fishPointer/Joule-Thief/LTSpice/Joule Thief R4 V1.asc

C1: cap; 1µ
C2: cap; 10µ
C3: cap; 4.7µ
C4: cap; 10µ
C5: cap; 50m
C6: cap; 10n
D1: diode
D2: diode
D3: schottky; 1N5817
I1: current; {ISOURCE}
I2: current; {ISINK}
L1: ind; 20µ; Rser=1.87
M1: pmos; IRF9540N
R1: res; 900k
R2: res; 220k
R3: res; 47k
R4: res; 0.1
R5: res; 100k
R6: res; 0.1
R7: res; 4.7k
R8: res; 100k
R9: res; 75k
R10: res; 100
U1: LTC3105
U2: TL431
U3: lm393
V1: voltage; 1.2; Rser=0
V2: voltage; 0
Named nets: 0, IN, LDO, FB, OUT, vb
Joule Thief R4 V1 - MVP
.param ISINK=1m
.param ISOURCE=1
CURRENT LIMITED VOLTAGE SOURCE
.tran 1 startup
18650 Li-Ion Cell
AA 1.5V Alkaline Cell
4.3V Overcharge Protect
Dummy Load for testing
MPPC Resistor
AA ESR
Dummy Load for testing
