fishPointer/Joule-Thief/LTSpice/Accessory Circuits/Barebones BMS R0 - Comparators.asc

C1: cap; 10µ
LED1: diode; 1N914
LED: diode; 1N914
R1: res; 220
R2: res; 100
R3: res; 50k
R4: res; 220
R5: res; 500
R6: res; 50k
R7: res; 220
R8: res; 220
R9: res; 500
R10: res; 500
R11: res; 1k
R12: res; 220
R13: res; 1k
R14: res; 1k
R15: res; 1k
U1: TL431
U2: lm393
U3: 1N4728A
U4: lm393
U5: 1N4731A
U6: irf4905
U7: irfz44n
U8: LM358
U9: TL431
U10: lm393
V1: voltage; 4.2
V2: voltage; SINE(2.5 2.5 500)
V3: voltage; SINE(3 3 500)
V4: voltage; SINE(2.5 2.5 500)
Named nets: 0, VCC, VOUT, V431
.tran 20m
