fishPointer/Joule-Thief/LTSpice/Accessory Circuits/Charge and Discharge Protection R1V1.asc

C1: cap; 10n
C2: cap; 10n
M1: pmos; Si9433DY
M2: pmos; Si9433DY
M3: pmos; Si9433DY
M4: pmos; Si9433DY
R1: res; 10k
R2: res; 5k
R3: res; 1000
R4: res; 1400
R5: res; 100
R6: res; 220
R7: res; 50k
R8: res; 10
R9: res; 10
R10: res; 100
R11: res; 5k
R12: res; 10k
R13: res; 1000
R14: res; 1400
R15: res; 220
R16: res; 50k
U1: TL431
U2: lm393
U3: TL431
U4: lm393
V1: voltage; PULSE(0 5 0 20m 20m 20m 80m)
V2: voltage; 5
V3: voltage; 4.3
V4: voltage; PULSE(0 5 0 20m 20m 20m 80m)
V5: voltage; 5
V6: voltage; 4.3
Named nets: 0, VB, VA
.tran 80m startup
