fishPointer/Joule-Thief/LTSpice/Accessory Circuits/Charge and Discharge Protection R1V2.asc

C1: cap; 10n
M1: pmos; Si9433DY
M2: pmos; Si9433DY
R1: res; 10
R2: res; 100
R3: res; 5k
R4: res; 10k
R5: res; 1000
R6: res; 1400
R7: res; 220
R8: res; 50k
U1: TL431
U2: lm393
V1: voltage; PULSE(0 5 0 20m 20m 20m 80m)
V2: voltage; 5
V3: voltage; 4.3
Named nets: 0, VB, VA
.tran 100m
