fishPointer/Joule-Thief/LTSpice/Accessory Circuits/Current Limited Voltage Source.asc

C1: cap; 1µ
D1: diode
D2: diode
I1: current; {ISOURCE}
I2: current; {ISINK}
R1: res; 1k
V1: voltage; PULSE(0 10 0 1n 1n 1m 2m)
Named nets: 0
.param ISINK=1m
.param ISOURCE=1m
.tran 20m
CURRENT LIMITED VOLTAGE SOURCE
