fishPointer/Joule-Thief/LTSpice/Accessory Circuits/LM324 Output Impedance.asc

R1: res; 2k
R2: res; 2k
U1: LM324
U2: pot; T=0
U3: LM324
V2: voltage; 15
V3: voltage; 15
V_TEST1: voltage; SINE(); AC 1
V_TEST: voltage; SINE(); AC 1
Named nets: 15V, 0, -15V, V_OUT
.tran 0 20m 0 1m
.ac dec 100 0.1 100k
