fishPointer/Joule-Thief/LTSpice/Accessory Circuits/LM358 Schmitt Trigger V1.asc

M1: pmos
M2: nmos
R1: EuropeanResistor; 2k
R2: EuropeanResistor; 2k
R3: EuropeanResistor; 2k
R4: EuropeanResistor; 2k
R5: res; 1k
U1: LM358
V1: voltage; 5
V2: voltage; PULSE(0 5 0 50u 50u 10u 120u)
V3: voltage; 3.5
Named nets: 5V, 0, OUT, pulse
.tran 1m startup
