fishPointer/Joule-Thief/LTSpice/Accessory Circuits/LM386 Input Impedance.asc

C1: cap; 100µ
C2: cap; 100µ
C3: cap; 100n
C4: cap; 1000µ
R1: res; 8
U1: Lm386
U3: speaker
V1: voltage; 12
V2: voltage; SINE(0 1 1000); AC 1
Named nets: 0
LM386 AUDIO AMPLIFIER
.tran 0 10m 0 10u
.param T=0.5
.ac dec 100 1 100k
