fishPointer/Joule-Thief/LTSpice/Accessory Circuits/LM393 Schmitt Trigger V1.asc

C1: polcap; 1000µ; V=10 Irms=520m Rser=0.112 Lser=22.8n mfg="Würth Elektronik" pn="860020275015 WCAP-ATG5 10x12,5" type="Al electrolytic"
I1: current; 0.01
M2: pmos; AO6407
R1: res; 10k
R2: res; 30k
R4: res; 100
Rs: res; 5k
U1: lm393
U2: opamp
V2: voltage; 4.2
Named nets: 0, VCC
.tran 2 startup
.param Rp =(R1/R2)
.param R1=10k
.param R2=3.3k
BATTERY EXTRACTION MODULE
SAMPLING CAPACITOR VOLTAGE
FEEDING BACK INTO SCHMITT TRIGGER
SET SCHMITT TRIGGERS AT 1V, 4V
SCHMITT OUTPUT TOGGLES PMOS SWITCH
BMS HANDLES PULSE
