fishPointer/Joule-Thief/LTSpice/Accessory Circuits/NMOS Enable Switch Sketch.asc

M1: pmos; AO6407
R3: res; 10k
R_Load: res; 500
U1: 2N7000
V1: voltage; PULSE(0 5 0 1n 1n 10m 20m)
V2: voltage; 5
Named nets: 5V, 0, GPIO, out_n, out_p
.tran 100m
