fishPointer/Joule-Thief/LTSpice/Accessory Circuits/Rechargeable Battery V1.asc

B1: bi; I=I(V4)
BATT: bv; V=vbatt(V(vsoc))
CAP: cap; 100 IC=5; V=100
D1: diode
D2: diode
D3: diode
D4: diode
D5: diode
D6: diode
I1: current; PULSE(10 -2 0 1 1 20 30)
R2: res; 1Meg
R3: res; 10m
R4: res; 20m
V2: voltage; 100
V3: voltage; 4.3
V4: voltage; 0
Named nets: 0, vsoc, vbatt
.tran 0 10k 0
.func vbatt(vsoc) (2.44544e-9*pwr(vsoc,5) - 6.00106e-7*pwr(vsoc,4) + 0.000060708*pwr(vsoc,3) - 0.00307689*pwr(vsoc,2) + 0.0774173*vsoc + 2.48387)
RECHARGEABLE BATTERY
