fishPointer/Joule-Thief/LTSpice/Accessory Circuits/Schmitt Trigger for Cap Pulse V0.asc

Q1: npn
Q2: npn
Q3: npn
Q4: npn
R1: res; 1k
R2: res; 16k
R3: res; 4k
R4: res; 1k
R5: res; 100k
R6: res; 1k
R7: res
R8: res
R9: res
R10: res
R11: res
V1: voltage; 5
V2: voltage; SINE(5 5 100)
V3: voltage; PULSE(0 6 0 50m 50m 10m 120m)
V4: voltage
Named nets: 0, 5V, IN, OUT
.tran 120m startup
