fishPointer/Joule-Thief/LTSpice/Accessory Circuits/TL431.asc

R1: res; 240
R2: res; 100
R3: res; 500
U1: TL431
V1: voltage; PULSE(0 10 0 10m 1n 0 11m)
Named nets: 0
.tran 50m startup
