fishPointer/Joule-Thief/LTSpice/Main Versions/Joule Thief MVP R2 V2.asc

C1: cap; 1µ
C2: cap; 10µ
C3: cap; 4.7µ
C4: cap; 10µ
D2: diode
D3: diode
I1: current; {ISOURCE}
I2: current; {ISINK}
L1: ind; 10µ
R1: res; 40.2k
R2: res; 800k
R3: res; 200k
R4: res; 150
U1: LTC3105
U2: 1N4733A
V2: voltage; 0.725
V3: voltage; 0
Named nets: 0, IN, LDO, FB, OUT
Joule Thief R2 V0 - MVP
.param ISINK=1m
.param ISOURCE=500m
CURRENT LIMITED VOLTAGE SOURCE
.tran 100m
