fishPointer/Joule-Thief/LTSpice/Main Versions/Joule Thief R0 V3.asc

C1: cap; 10µ
C3: cap; 10µ
D1: LED; NSPW500BS
D2: schottky; 1N5818
D3: schottky; MBR0520L
D4: schottky; MBRS140
D5: schottky; MBRS140
D6: diode; 1N4148
D7: LED; NSPW500BS
D8: diode
L1: ind; 47µ
Lp: ind2; {Lxf}; Rser=0.176
Ls: ind2; {Lxf}; Rser=0.176
Q1: npn; 2N2222
R1: res; 1k
R2: RES; 300K
R3: RES; 13.8k
R4: res; 2000
R5: res; 1k
U1: LT1110
U2: LM113
V1: voltage; 1.5
V3: voltage; 1.3861; Rser=0.5
Named nets: 0, Vbe, VOUT, VLOAD, CAP, BATT
K1 Lp Ls 0.98
.param Lxf = 100u
;.step dec param Lxf 100u 1 3
.meas TRAN AvgPwr AVG (V(VLOAD)*I(D1))
.meas Toroid param Lxf
.MEAS TRAN TPERIOD1 WHEN V(OUT)=0.5 RISE=1
.MEAS TRAN TPERIOD2 WHEN V(VOUT)=0.5 RISE=2
.MEAS TRAN FREQ PARAM 1/(TPERIOD2-TPERIOD1)
.meas TRAN AvgLoss AVG (V(VOUT)*Ie(Q1))
.param Vbatt = 1V
;.step param Vbatt 0.1 1.0 0.1
.meas tran Battery param Vbatt
.tran 0 50m 0 startup
.meas TRAN IBase PARAM I(R1)
.meas tran V_BE param V(Vbe)
JOULE THIEF R0 V3
.meas TRAN AvgDischarge AVG (I(V3))
CONFIG 1
