fishPointer/Joule-Thief/LTSpice/Main Versions/Joule Thief R0.asc

C1: cap; 10µ
D1: LED; NSPW500BS
D2: schottky; 1N5818
Lp: ind2; {Lxf}
Ls: ind2; {Lxf}
Q1: npn; 2N2222
R1: res; 500
V1: voltage; {Vbatt}
Named nets: 0, Vbe
.tran 0 25m 0
K1 Lp Ls 0.98
Basic Joule Thief R0 V2
.param Lxf = 100u
;.step dec param Lxf 1u 1m 3
.meas tran AvgPwr AVG (V(N003)*I(D1))
.meas Toroid param Lxf
.MEAS TRAN TPERIOD1 WHEN V(n003)=0.5 RISE=1
.MEAS TRAN TPERIOD2 WHEN V(n003)=0.5 RISE=2
.MEAS TRAN FREQ PARAM 1/(TPERIOD2-TPERIOD1)
.meas tran AvgLoss AVG (V(N003)*Ie(Q1))
.param Vbatt = 1V
;.step param Vbatt 0.1 1.0 0.1
.meas TRAN IBase PARAM I(R1)
.meas tran Battery param Vbatt
.meas tran V_BE param V(Vbe)
