fishPointer/Joule-Thief/LTSpice/Main Versions/Joule Thief R1 V0.asc

C1: cap; 10µ
C2: cap; 4.7µ
C3: cap; 1µ
C4: cap; 10µ
L1: ind; 10µ
R1: res; 40.2k
R2: res; 1020k
R3: res; 200k
U1: LTC3105
V_BATT: voltage; 1
Named nets: 0, IN, LDO, FB, OUT
Joule Thief R1 V0
.tran 10m startup
