fishPointer/Joule-Thief/LTSpice/Main Versions/Joule Thief R3 V2.asc

C1: cap; 1µ
C2: cap; 10µ
C3: cap; 4.7µ
C4: cap; 10µ
C5: cap; 100µ
D1: diode
D2: diode
D3: schottky; 1N5817
I1: current; {ISOURCE}
I2: current; {ISINK}
L1: ind; 10µ
Lp: ind2; {Lxf}; Rser=0.176
Ls: ind2; {Lxf}; Rser=0.176
Q1: npn; 2N2222
R1: res; 800k
R2: res; 200k
R3: res; 100
R4: res; 0.1
R5: res; 40k
R6: res; 1k
U1: LTC3105
U2: 1N4728A
V1: voltage; 1; Rser=0
V2: voltage; 0
Named nets: 0, IN, LDO, FB, OUT, Vbe, BATT
Joule Thief R3 V2 - MVP
.param ISINK=1m
.param ISOURCE=1
CURRENT LIMITED VOLTAGE SOURCE
.tran 250m startup
K1 Lp Ls 0.98
.param Lxf = 100u
