fishPointer/Joule-Thief/LTSpice/Main Versions/Joule Thief R4 V0.asc

C1: cap; 1µ
C2: cap; 10µ
C3: cap; 4.7µ
C4: cap; 10µ
C5: cap; 10n
C6: cap; 1m
D1: diode
D2: diode
D3: schottky; 1N5817
I1: current; {ISOURCE}
I2: current; {ISINK}
L1: ind; 20µ; Rser=1.87
M2: pmos; IRF9540N
M3: pmos; IRF7204
R1: res; 900k
R2: res; 220k
R3: res; 0.1
R4: res; 0.1
R5: res; 40k
R7: res; 100
R8: res; 4.7k
R9: res; 10k
R10: res; 10k
R11: res; 14.7k
R12: res; 220
R13: res; 47k
U1: LTC3105
U2: TL431
U3: lm393
V1: voltage; 1.5; Rser=0
V2: voltage; 0
Named nets: 0, IN, LDO, FB, OUT, VB
Joule Thief R4 V0 - MVP
.param ISINK=1m
.param ISOURCE=1
CURRENT LIMITED VOLTAGE SOURCE
.tran 1 startup
overdischarge protect
overcharge protect
load
battery
