fishPointer/Joule-Thief/Arduino/Joule_Chief/Drafts/LTC3105_Static_Load_Test_1/LTC3105_Static_Load_Test_1.ino

//CHANNEL A

#include <Wire.h>
#include "AD524X.h"

// INA219 Configuration
const uint8_t INA219_ADDR_1 = 0x40;         // Default address (A0=GND, A1=GND)
const uint8_t INA219_ADDR_2 = 0x41;         // Alternative address (A0=VDD, A1=GND)
const uint16_t INA219_CONFIG = 0x05DF;      // Configuration register value
const uint16_t INA219_CALIBRATION = 0x2000; // Calibration register value

// LSB (Least Significant Bit) constants for measurements
const float CURRENT_LSB = 0.000050;        // 50µA per bit
const float POWER_LSB = 20 * CURRENT_LSB;  // ~2mW per bit
const float V_SHUNT_LSB = 0.000010;        // 10µV per bit
const float V_BUS_LSB = 0.004;             // 4mV per bit

// AD5280 Digital Potentiometer
AD5280 AD01(0x2C);  // AD0 & AD1 == GND
float mppcValue = 1.0;  // Global float to store the MPPC value

// Global variables for efficiency calculation
float powerIn = 0.0;
float powerOut = 0.0;
float efficiency = 0.0;
// Global variables for hill climbing algorithm
float lastEfficiency = 0.0;
float stepSize = 0.05;        // MPPC adjustment step size
int direction = 1;            // 1 for increasing, -1 for decreasing
unsigned long lastAdjustment = 0;
const unsigned long adjustmentInterval = 500; // Adjust every 500ms
float currentSourceVoltage = 0.0;  // Store current source voltage
bool mppcEnabled = false;     // Track if MPPC algorithm is enabled

// ────────────────────────── Function Declarations ──────────────────────────

uint16_t readReg16(uint8_t addr, uint8_t reg);
void writeReg16(uint8_t addr, uint8_t reg, uint16_t value);
bool isConversionReady(uint8_t addr);
float readBusVoltage(uint8_t addr);
float readShuntVoltage(uint8_t addr);
float readCurrent(uint8_t addr);
float readPower(uint8_t addr);
void dumpRegisters(uint8_t addr);
void setMPPC(float targetVoltage);
void hillClimbMPPC();

// ─────────────────────────── Setup ───────────────────────────

void setup() {
  Serial.begin(115200);
  Wire.begin();
  Wire.setClock(400000);  // Set I2C clock to 400kHz for all devices

  // Initialize AD5280 digital potentiometer
  bool adConnected = AD01.begin();
  Serial.print(F("AD5280 connected: "));
  Serial.println(adConnected ? F("true") : F("false"));
  Serial.print(F("AD5280 isConnected: "));
  Serial.println(AD01.isConnected());

  // Configure first INA219
  writeReg16(INA219_ADDR_1, 0x00, INA219_CONFIG);      // Config register
  writeReg16(INA219_ADDR_1, 0x05, INA219_CALIBRATION); // Calibration register

  // Configure second INA219 (uncomment if using second sensor)
  writeReg16(INA219_ADDR_2, 0x00, INA219_CONFIG);      // Config register
  writeReg16(INA219_ADDR_2, 0x05, INA219_CALIBRATION); // Calibration register

  Serial.println(F("INA219 initialized"));
  Serial.println(F("All I2C devices ready"));
}

// ─────────────────────────── Main Loop ───────────────────────────

void loop() {
  // Read input measurements from sensor 1
  if (isConversionReady(INA219_ADDR_1)) {
    float sourceVoltage = readBusVoltage(INA219_ADDR_1);
    currentSourceVoltage = sourceVoltage;  // Store for hill climbing constraint
    float currentIn = readCurrent(INA219_ADDR_1);
    powerIn = readPower(INA219_ADDR_1);
    
    // Check if MPPC should be enabled/disabled based on source voltage
    if (currentSourceVoltage >= 0.3) {
      mppcEnabled = true;
    } else {
      mppcEnabled = false;
    }
    
    Serial.print("source_voltage=");
    Serial.print(sourceVoltage, 2);
    Serial.print(",power_in=");
    Serial.print(powerIn * 1000, 2);  // Convert to mW
    Serial.print(",current_in=");
    Serial.print(currentIn * 1000, 2); // Convert to mA
    Serial.print(",mppc=");
    Serial.print(mppcValue, 2);
    Serial.print(",mppc_enabled=");
    Serial.print(mppcEnabled ? 1 : 0);
    Serial.println();
  }
  
  // Read output measurements from sensor 2
  if (isConversionReady(INA219_ADDR_2)) {
    float boostVoltage = readBusVoltage(INA219_ADDR_2);
    float currentOut = readCurrent(INA219_ADDR_2);
    powerOut = readPower(INA219_ADDR_2);
    
    // Calculate efficiency
    efficiency = powerOut/powerIn * 100.0;
    
    Serial.print("boost_voltage=");
    Serial.print(boostVoltage, 2);
    Serial.print(",power_out=");
    Serial.print(powerOut * 1000, 2); // Convert to mW
    Serial.print(",current_out=");
    Serial.print(currentOut * 1000, 2); // Convert to mA
    Serial.print(",efficiency=");
    Serial.print(efficiency, 6);
    Serial.println();
    
    // Hill climbing algorithm - only run if enabled and timing is right
    if (mppcEnabled && millis() - lastAdjustment > adjustmentInterval) {
      hillClimbMPPC();
      lastAdjustment = millis();
    }
  }
}

// // Reads Serial Events coming from Dashboard. Looks for a float 0-2.0 and sets MPPC.
//   if (Serial.available()) {
//     String input = Serial.readStringUntil('\n');
//     if (input.length() > 0) {
//       mppcValue = input.toFloat();  // Save to global variable
//       setMPPC(mppcValue);           // Pass to function
//     }
//   }



// ────────────────────────── Function Definitions ──────────────────────────

/* Read 16-bit register from INA219 */
uint16_t readReg16(uint8_t addr, uint8_t reg) {
  Wire.beginTransmission(addr);
  Wire.write(reg);
  Wire.endTransmission(false);              // Repeated start

  Wire.requestFrom(addr, (uint8_t)2);
  while (Wire.available() < 2);             // Wait for data

  uint16_t val = (uint16_t)Wire.read() << 8; // MSB
  val |= Wire.read();                        // LSB
  return val;
}

/* Write 16-bit value to INA219 register */
void writeReg16(uint8_t addr, uint8_t reg, uint16_t value) {
  Wire.beginTransmission(addr);
  Wire.write(reg);
  Wire.write((uint8_t)(value >> 8));        // MSB
  Wire.write((uint8_t)(value & 0xFF));      // LSB
  Wire.endTransmission();
}

/* Check if conversion is ready */
bool isConversionReady(uint8_t addr) {
  uint16_t rawBus = readReg16(addr, 0x02);  // Bus voltage register
  return rawBus & 0x0002;                   // Bit 1: Conversion Ready Flag
}

/* Read bus voltage in Volts */
float readBusVoltage(uint8_t addr) {
  uint16_t rawBus = readReg16(addr, 0x02);
  uint16_t busData = rawBus >> 3;           // Ignore 3 LSBs
  return busData * V_BUS_LSB;
}

/* Read shunt voltage in Volts */
float readShuntVoltage(uint8_t addr) {
  uint16_t rawShunt = readReg16(addr, 0x01);
  int16_t signedShunt = (int16_t)rawShunt;  // Handle two's complement
  return signedShunt * V_SHUNT_LSB;
}

/* Read current in Amps */
float readCurrent(uint8_t addr) {
  uint16_t rawCurrent = readReg16(addr, 0x04);
  int16_t signedCurrent = (int16_t)rawCurrent; // Handle two's complement
  return signedCurrent * CURRENT_LSB;
}

/* Read power in Watts */
float readPower(uint8_t addr) {
  uint16_t rawPower = readReg16(addr, 0x03);
  return rawPower * POWER_LSB;
}

/* Optional: Debug function to dump all registers */
void dumpRegisters(uint8_t addr) {
  uint16_t cfg  = readReg16(addr, 0x00);
  uint16_t shnt = readReg16(addr, 0x01);
  uint16_t bus  = readReg16(addr, 0x02);
  uint16_t pwr  = readReg16(addr, 0x03);
  uint16_t cur  = readReg16(addr, 0x04);
  uint16_t cal  = readReg16(addr, 0x05);

  Serial.print(F("INA219 Registers - CFG:0x"));
  Serial.print(cfg, HEX);
  Serial.print(F(" SHUNT:0x"));
  Serial.print(shnt, HEX);
  Serial.print(F(" BUS:0x"));
  Serial.print(bus, HEX);
  Serial.print(F(" PWR:0x"));
  Serial.print(pwr, HEX);
  Serial.print(F(" CUR:0x"));
  Serial.print(cur, HEX);
  Serial.print(F(" CAL:0x"));
  Serial.print(cal, HEX);
  Serial.println();
}

/* Set MPPC voltage by adjusting digital potentiometer
 * targetVoltage: Target voltage in range 0.0 to 2.0V
 * Maps voltage to digital pot value (0-256) and writes to AD5280
 */
void setMPPC(float targetVoltage) {
  // Clamp input to valid range
  if (targetVoltage < 0.0) targetVoltage = 0.0;
  if (targetVoltage > 2.0) targetVoltage = 2.0;
  
  // Map 0-2.0V range to 0-256 range
  float mapped = targetVoltage * 256.0 / 2.0;  // Simplified: targetVoltage * 128.0
  int potValue = (int)mapped;
  
  // Ensure we don't exceed the AD5280's maximum value (typically 255 or 256)
  if (potValue > 255) potValue = 255;
  
  // Write to digital potentiometer
  AD01.write(potValue);
}


void hillClimbMPPC() {
  // Calculate maximum allowed MPPC value (sourceVoltage - 0.2V)
  float maxAllowedMPPC = currentSourceVoltage - 0.2;
  
  // Check if efficiency improved from last adjustment
  if (efficiency > lastEfficiency) {
    // Keep going in the same direction
    mppcValue += direction * stepSize;
  } else {
    // Efficiency decreased, reverse direction
    direction *= -1;
    mppcValue += direction * stepSize;
  }
  
  // Constrain mppcValue to valid range with voltage constraint
  mppcValue = constrain(mppcValue, 0.0, min(maxAllowedMPPC, 2.0));
  
  // If we hit the voltage constraint, reverse direction for next iteration
  if (mppcValue >= maxAllowedMPPC) {
    direction = -1;  // Force downward direction
  }
  
  // Apply the new MPPC value
  setMPPC(mppcValue);
  
  // Store current efficiency for next comparison
  lastEfficiency = efficiency;
}
